hoanggtrn/Vehicle-Safety-Monitoring-And-Management-System/Báo cáo/Background trường.png

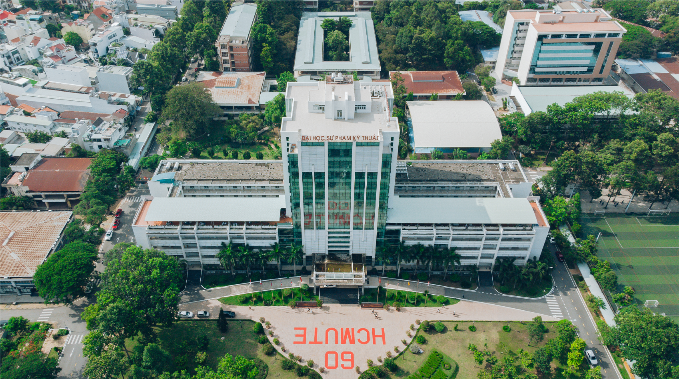
Báo cáo/Background trường.png
