hoanggtrn/Vehicle-Safety-Monitoring-And-Management-System/Báo cáo/Biểu đồ/Picture1.png

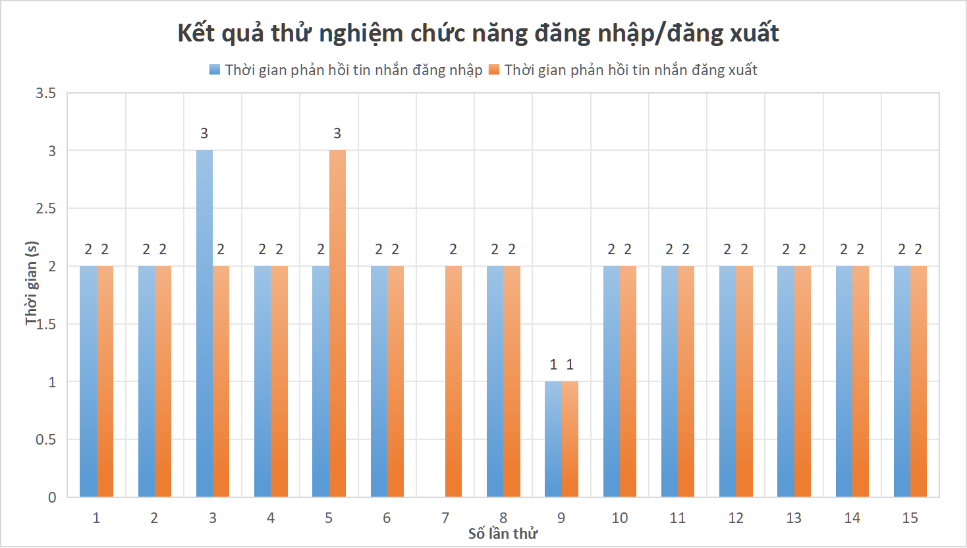
Báo cáo/Biểu đồ/Picture1.png
