hoanggtrn/Vehicle-Safety-Monitoring-And-Management-System/Báo cáo/Biểu đồ/Picture2.png

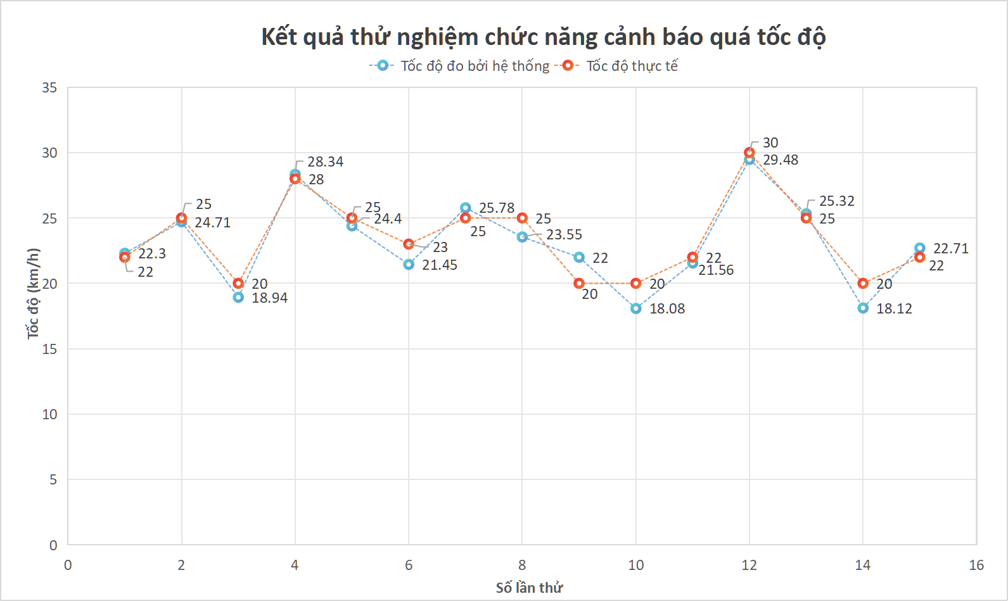
Báo cáo/Biểu đồ/Picture2.png
