hoanggtrn/Vehicle-Safety-Monitoring-And-Management-System/Báo cáo/Biểu đồ/Picture3.png

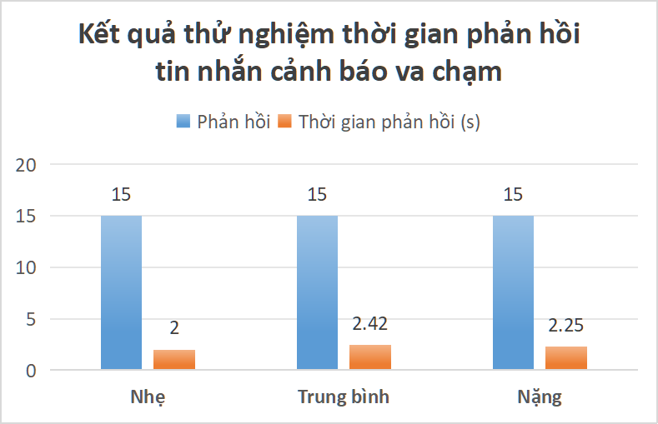
Báo cáo/Biểu đồ/Picture3.png
