hoanggtrn/Vehicle-Safety-Monitoring-And-Management-System/Báo cáo/Biểu đồ/Picture4.png

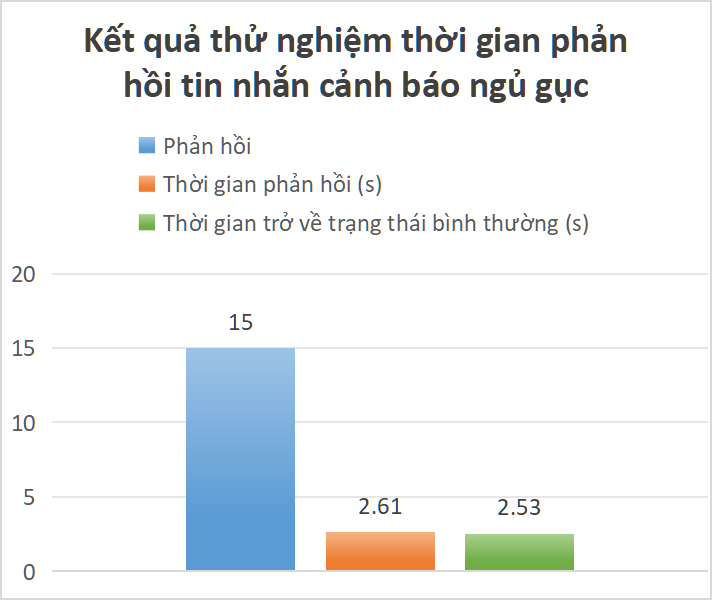
Báo cáo/Biểu đồ/Picture4.png
