hoanggtrn/Vehicle-Safety-Monitoring-And-Management-System/Báo cáo/Biểu đồ/Picture5.png

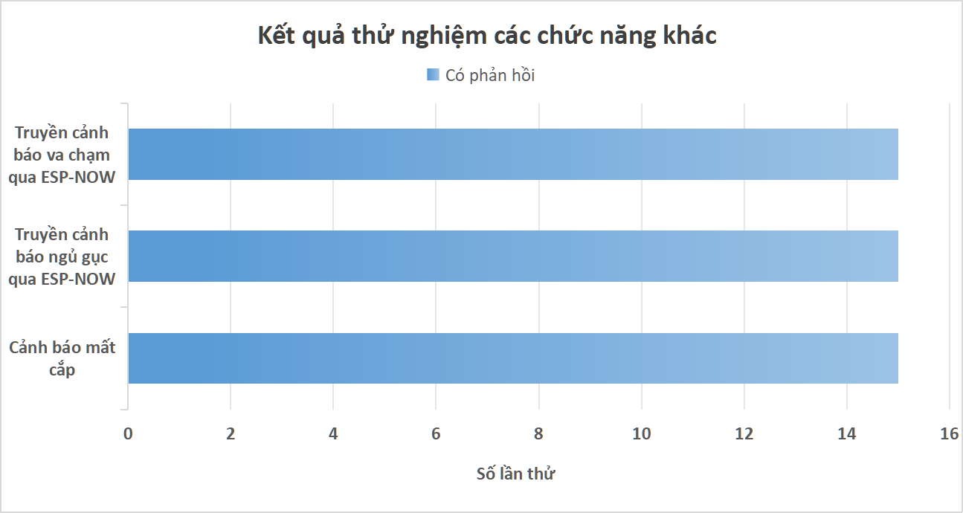
Báo cáo/Biểu đồ/Picture5.png
