hoanggtrn/Vehicle-Safety-Monitoring-And-Management-System/Báo cáo/Biểu đồ/Picture6.png

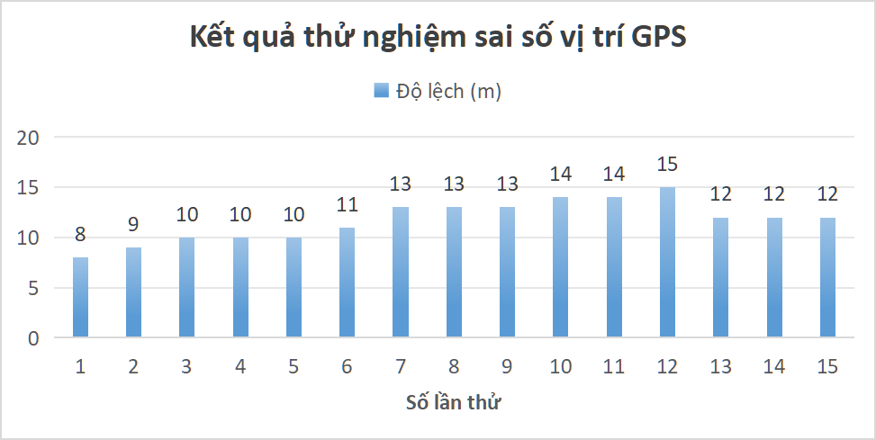
Báo cáo/Biểu đồ/Picture6.png
