hoanggtrn/Vehicle-Safety-Monitoring-And-Management-System/Báo cáo/Biểu đồ/Picture7.png

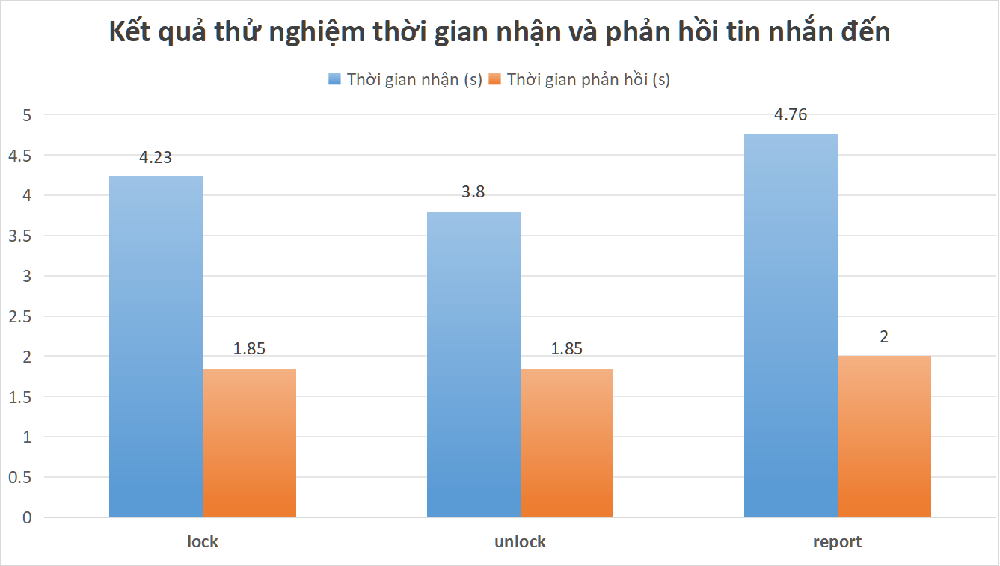
Báo cáo/Biểu đồ/Picture7.png
