hoanggtrn/Vehicle-Safety-Monitoring-And-Management-System/Báo cáo/Biểu đồ/Picture8.png

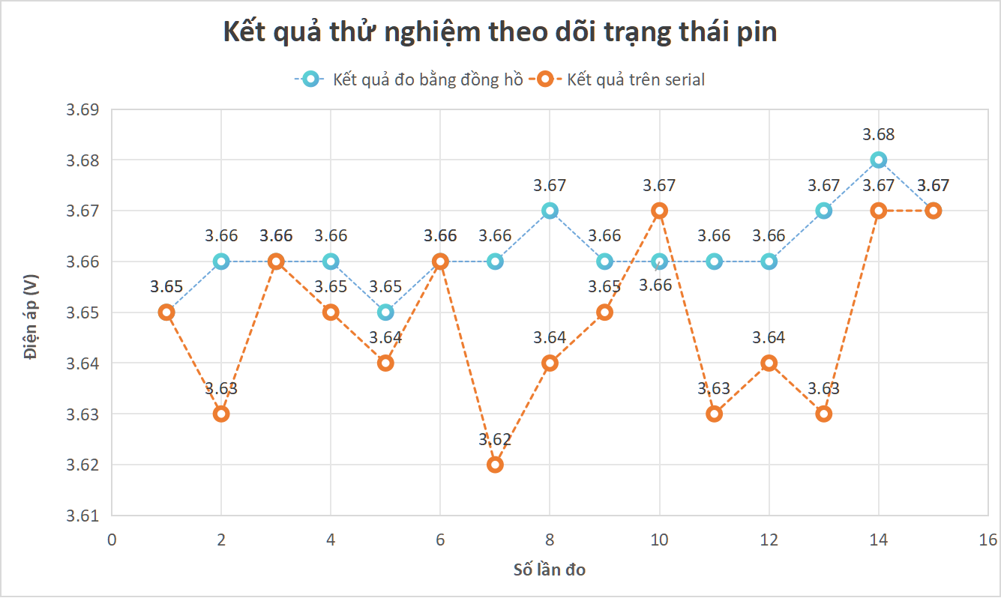
Báo cáo/Biểu đồ/Picture8.png
