hoanggtrn/Vehicle-Safety-Monitoring-And-Management-System/Thiết kế/Bộ cảnh báo ngủ gục/Mạch in/PCB_bocanhbaonguguc(back).png

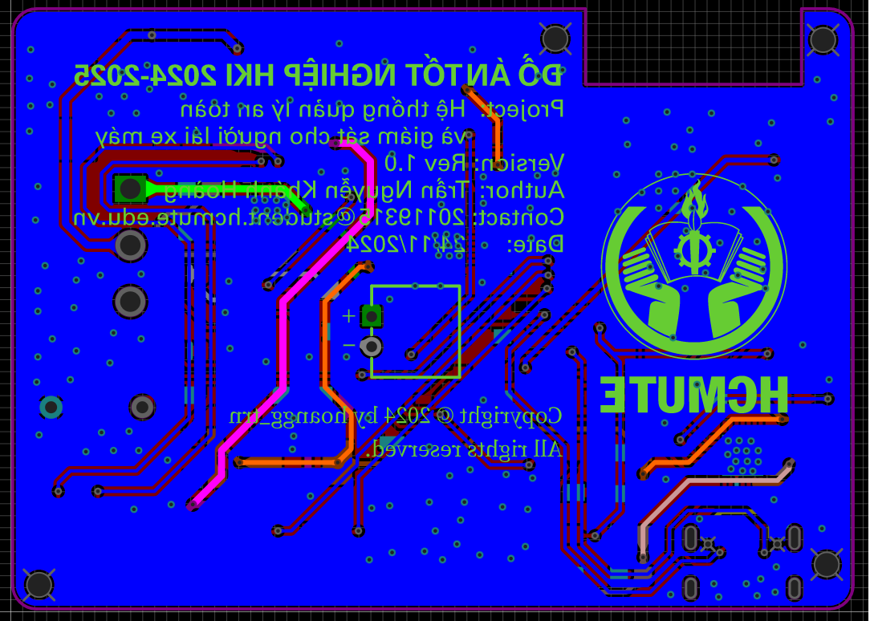
Thiết kế/Bộ cảnh báo ngủ gục/Mạch in/PCB_bocanhbaonguguc(back).png
