hoanggtrn/Vehicle-Safety-Monitoring-And-Management-System/Thiết kế/Bộ trung tâm/Mạch in/PCB_botrungtam(back).png

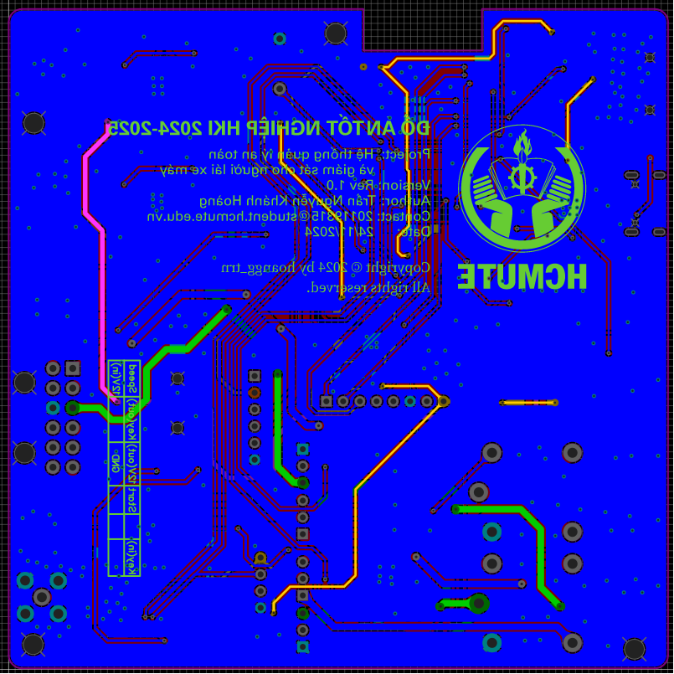
Thiết kế/Bộ trung tâm/Mạch in/PCB_botrungtam(back).png
