hoanggtrn/Vehicle-Safety-Monitoring-And-Management-System/Thiết kế/Bộ trung tâm/Schematic_Đồ-án-tốt-nghiệp_2024-11-26.png

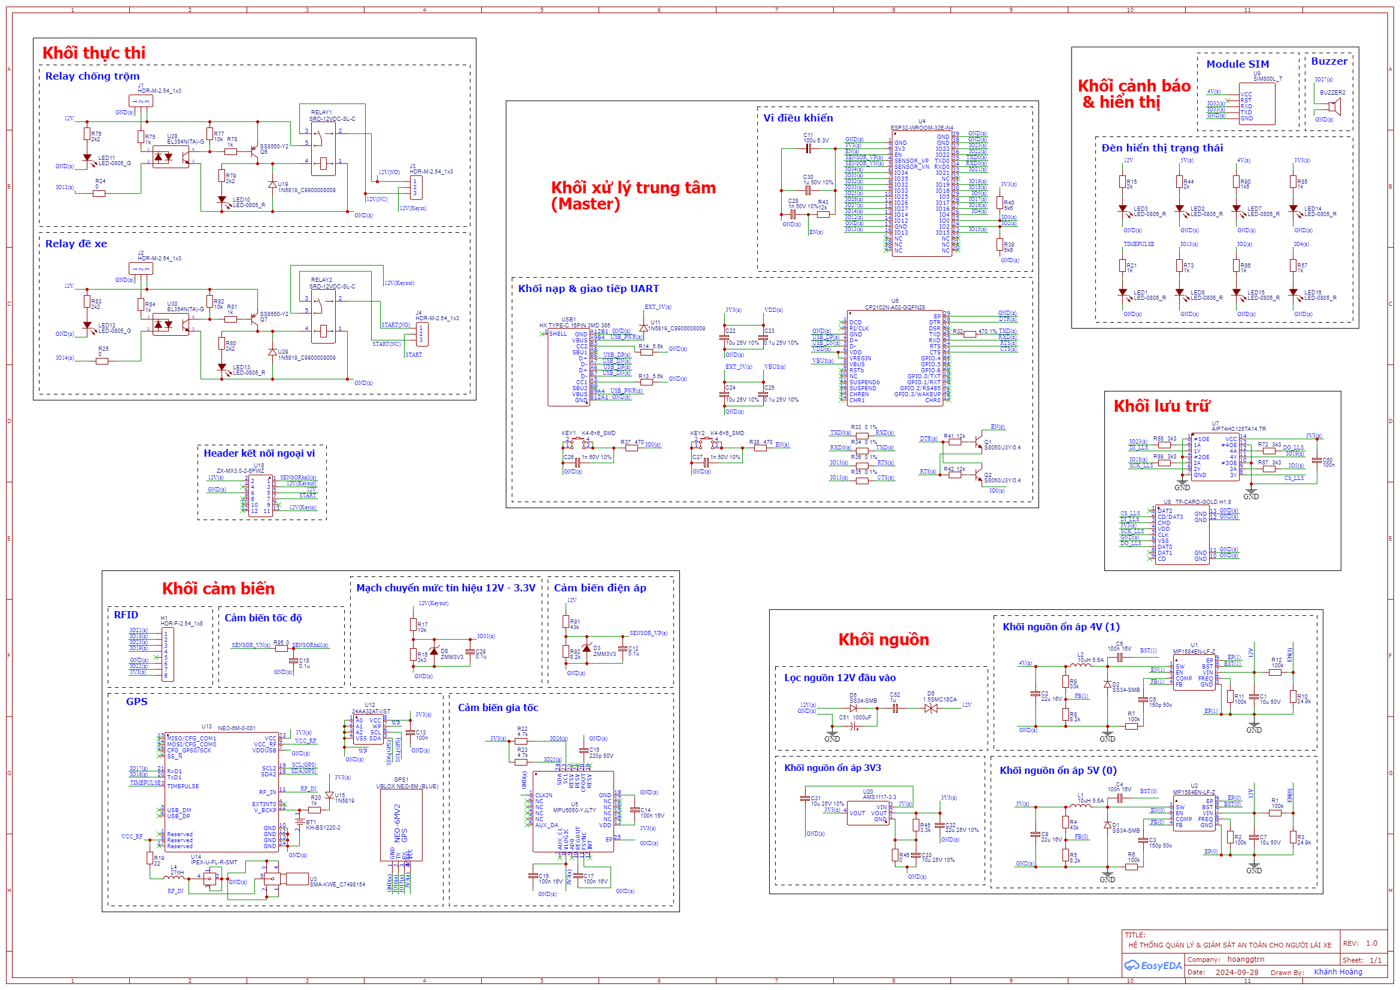
Thiết kế/Bộ trung tâm/Schematic_Đồ-án-tốt-nghiệp_2024-11-26.png
