hoanggtrn/Vehicle-Safety-Monitoring-And-Management-System/Thiết kế/Hình ảnh sản phẩm/P1011327.JPG

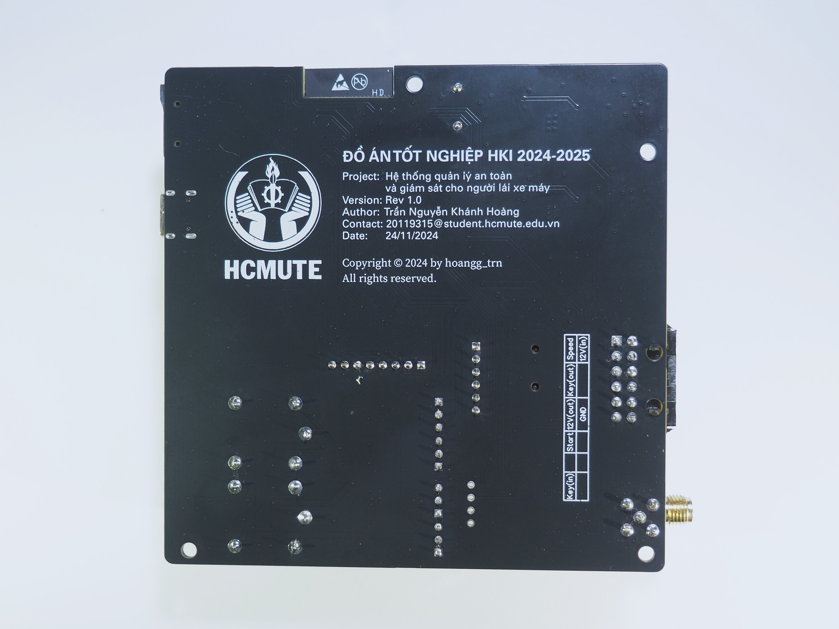
Thiết kế/Hình ảnh sản phẩm/P1011327.JPG
