hoanggtrn/Vehicle-Safety-Monitoring-And-Management-System/Thiết kế/Hình ảnh sản phẩm/P1011351.JPG

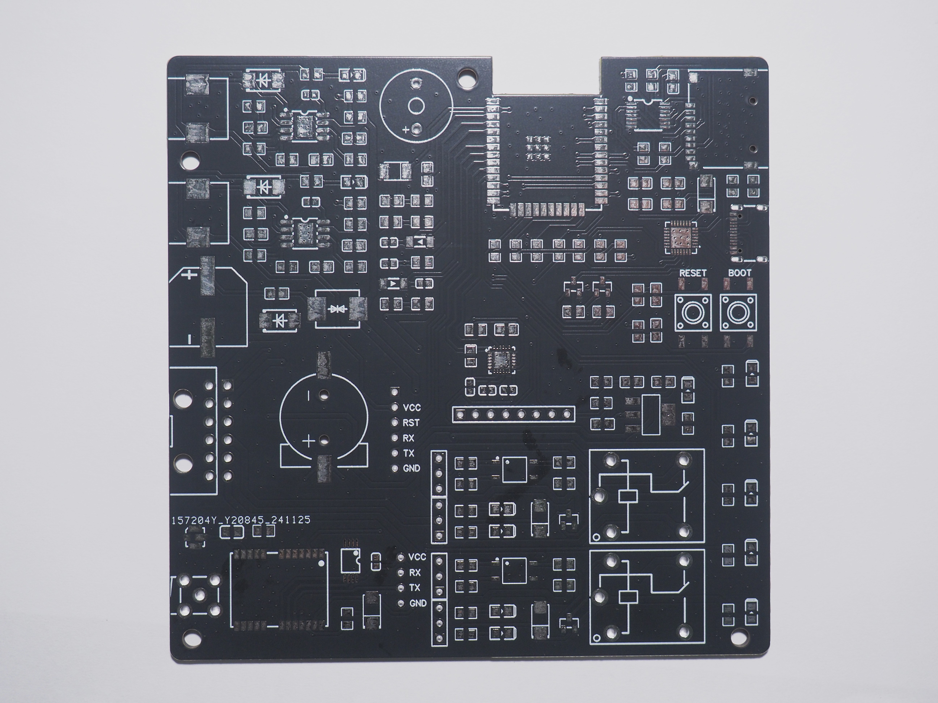
Thiết kế/Hình ảnh sản phẩm/P1011351.JPG
