hoanggtrn/Vehicle-Safety-Monitoring-And-Management-System/Thiết kế/sơ đồ phác thảo hệ thống.png

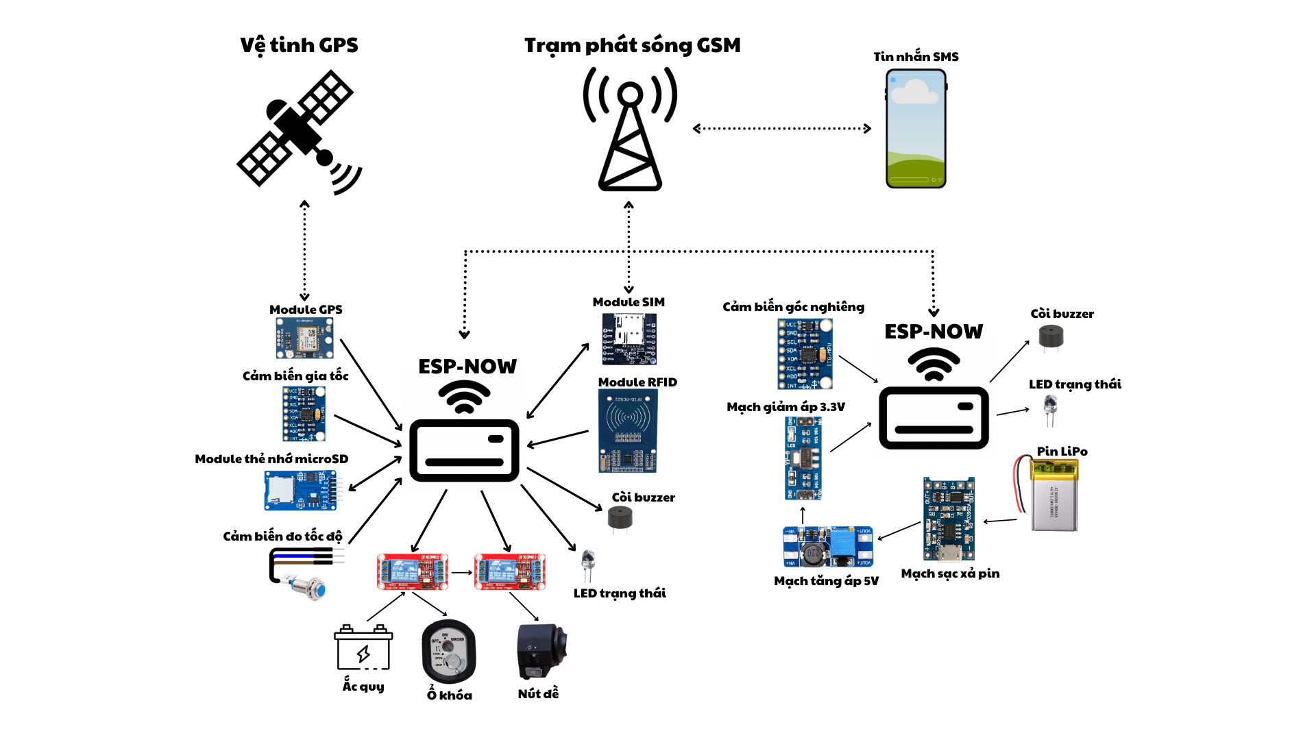
Thiết kế/sơ đồ phác thảo hệ thống.png
